rickyramnath97/gps/CENG355/Documentation/PCB.PNG

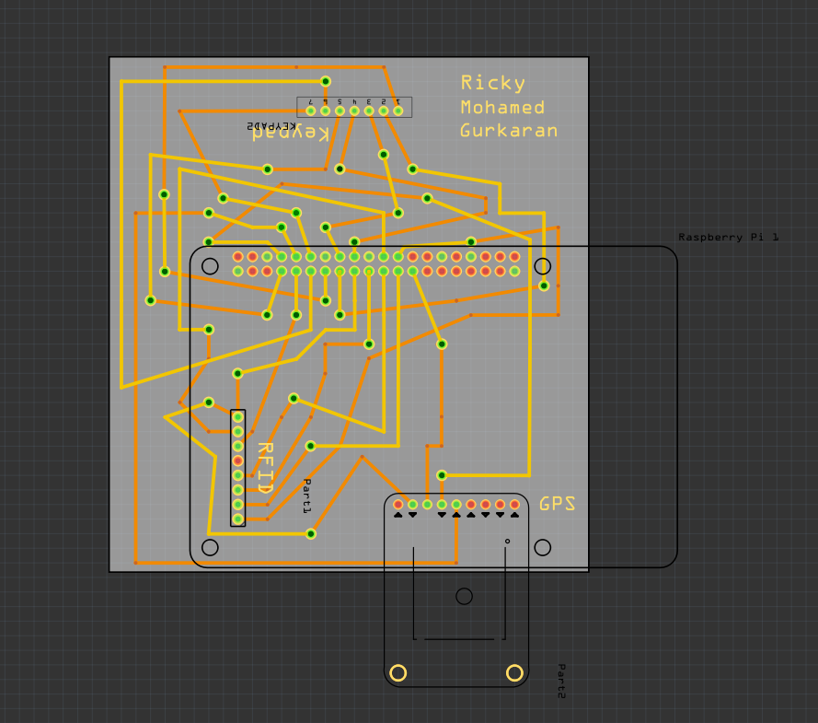
CENG355/Documentation/PCB.PNG
