rickyramnath97/gps/images/PCB.PNG

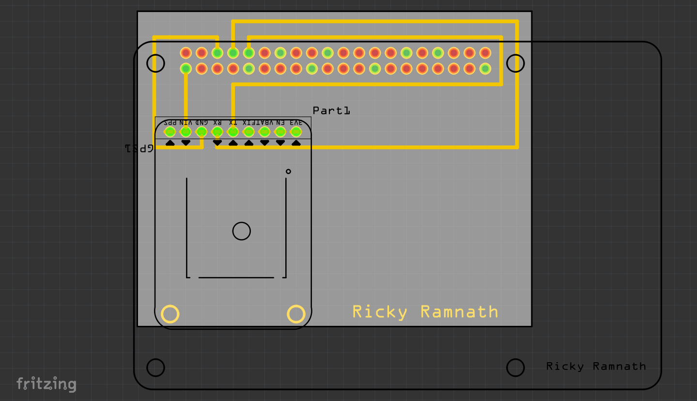
images/PCB.PNG
